obsdnx/prosthetics-summer-project/cad/varun-claw-mechanism/V2-Non-Equal-3-Segment-Hand/02 Full Assembly.SLDASM

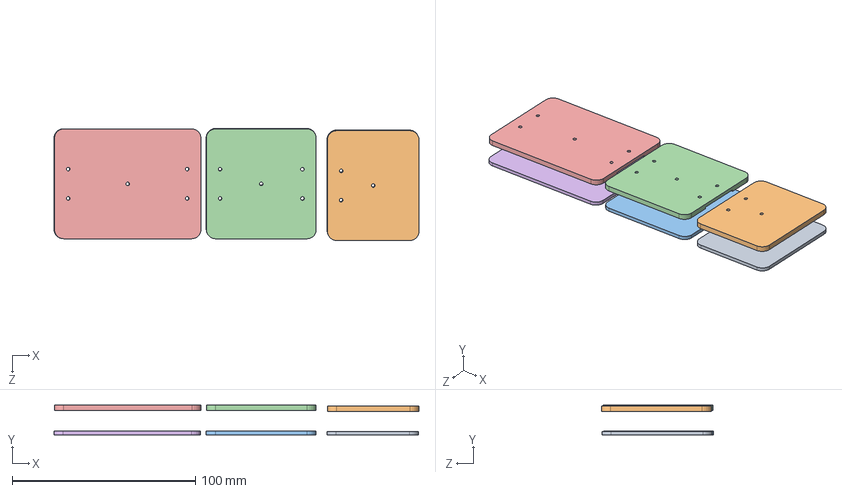
[picture p13: CAD file, 2026-07-27]
cad/varun-claw-mechanism/V2-Non-Equal-3-Segment-Hand/02 Full Assembly.SLDASM
199.4 x 16.4 x 61.2 mm
02-01 Start Segment Flat Side
02-02 Start Segment Hinge Side
02-03 Middle Segment Hinge Side
02-04 Middle Segment Flat Side
02-05 End Segment Hinge Side
02-06 End Segment Flat Side
