obsdnx/prosthetics-summer-project/cad/varun-claw-mechanism/V2-Wrist-Plate/04-01 Lower Wrist Plate.SLDPRT

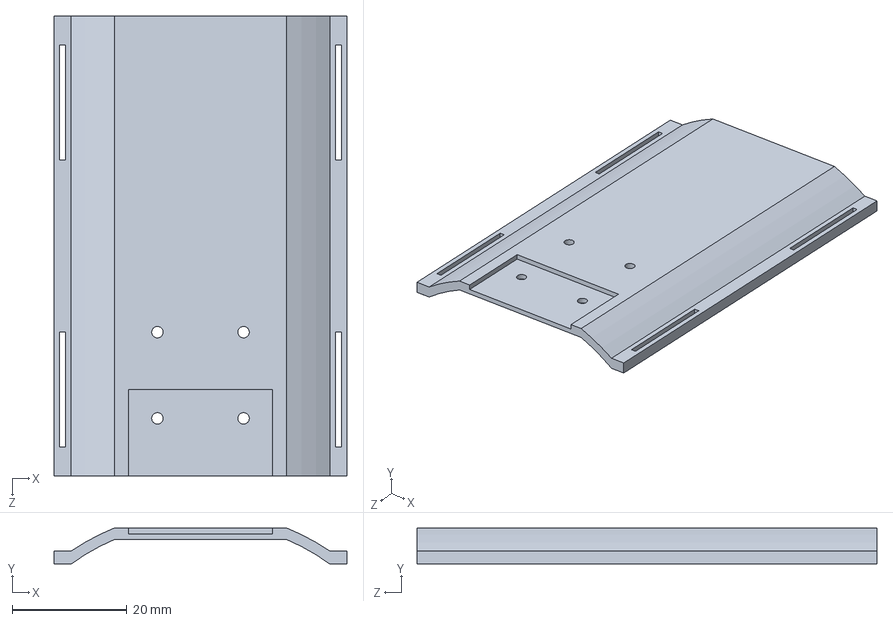
[picture p25: CAD file, 2026-07-27]
cad/varun-claw-mechanism/V2-Wrist-Plate/04-01 Lower Wrist Plate.SLDPRT
51.0 x 6.26 x 80.0 mm
