obsdnx/prosthetics-summer-project/cad/varun-claw-mechanism/V2-2-Segment-Hand/03-04 Start Segment Flat Side.SLDPRT

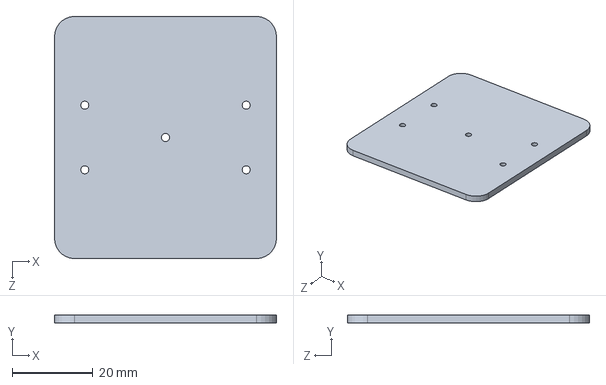
[picture p26: CAD file, 2026-07-27]
cad/varun-claw-mechanism/V2-2-Segment-Hand/03-04 Start Segment Flat Side.SLDPRT
55.0 x 2.00 x 60.0 mm
