obsdnx/prosthetics-summer-project/cad/varun-claw-mechanism/V2-Non-Equal-3-Segment-Hand/02-02 Start Segment Hinge Side.SLDPRT

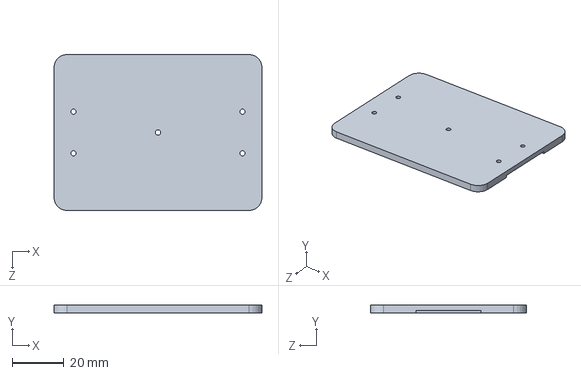
[picture p27: CAD file, 2026-07-27]
cad/varun-claw-mechanism/V2-Non-Equal-3-Segment-Hand/02-02 Start Segment Hinge Side.SLDPRT
80.0 x 3.00 x 60.0 mm
