obsdnx/prosthetics-summer-project/cad/varun-claw-mechanism/V2-Spring-Hinge-2/th-61sus-1_03.SLDPRT

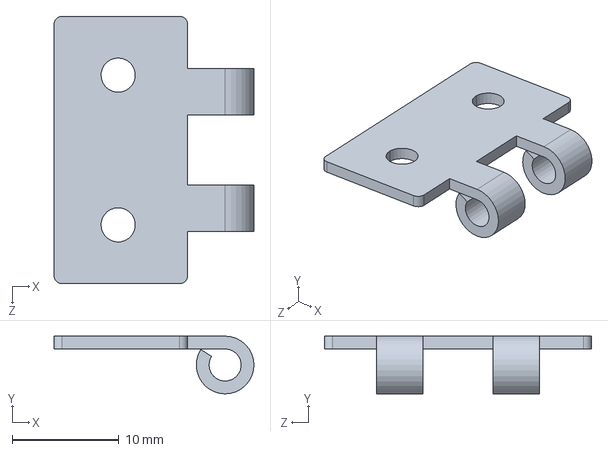
[picture p28: CAD file, 2026-07-27]
cad/varun-claw-mechanism/V2-Spring-Hinge-2/th-61sus-1_03.SLDPRT
18.7 x 5.40 x 25.0 mm
