obsdnx/prosthetics-summer-project/cad/varun-claw-mechanism/V2-Spring-Hinge/th-61-1_04.SLDPRT

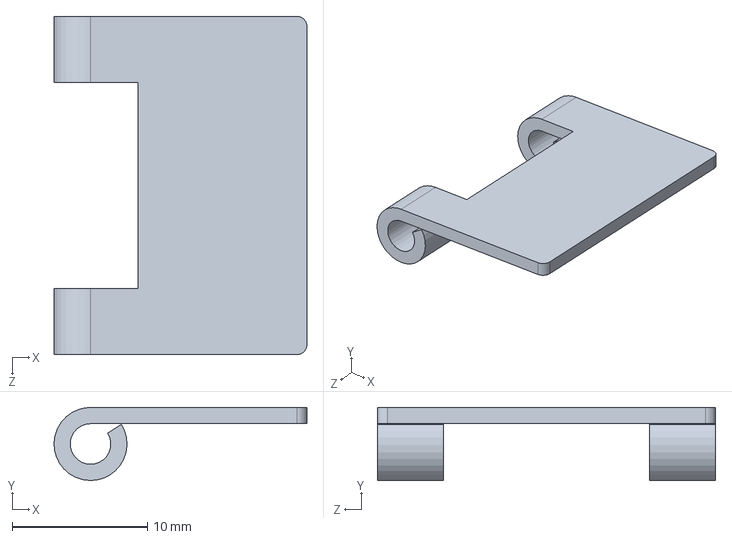
[picture p29: CAD file, 2026-07-27]
cad/varun-claw-mechanism/V2-Spring-Hinge/th-61-1_04.SLDPRT
18.7 x 5.40 x 25.0 mm
