obsdnx/prosthetics-summer-project/cad/varun-claw-mechanism/V2-Equal-3-Segment-Hand/01-02 End Plate Hinge Side.SLDPRT

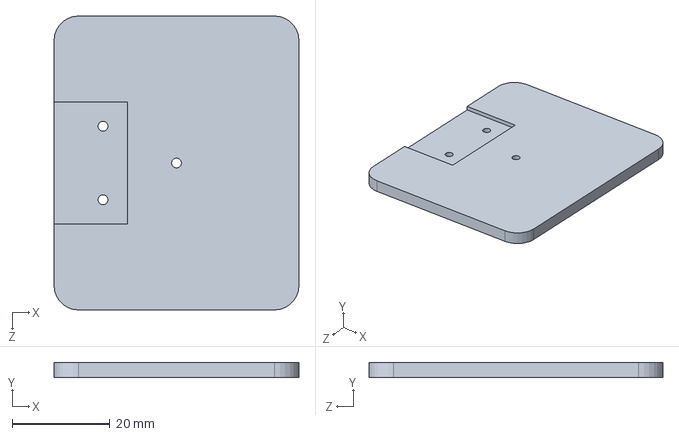
[picture p30: CAD file, 2026-07-27]
cad/varun-claw-mechanism/V2-Equal-3-Segment-Hand/01-02 End Plate Hinge Side.SLDPRT
50.0 x 3.00 x 60.0 mm
