obsdnx/prosthetics-summer-project/cad/varun-claw-mechanism/V2-Non-Equal-3-Segment-Hand/02-04 Middle Segment Flat Side.SLDPRT

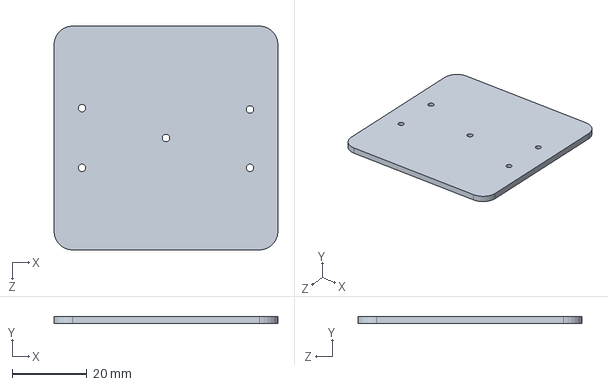
[picture p32: CAD file, 2026-07-27]
cad/varun-claw-mechanism/V2-Non-Equal-3-Segment-Hand/02-04 Middle Segment Flat Side.SLDPRT
60.0 x 2.00 x 60.0 mm
